korneelverraes/Ctrl-Wheely-2.0/software/album_a.jpg

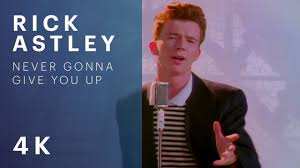
software/album_a.jpg
