korneelverraes/Ctrl-Wheely-2.0/software/album_b.jpg

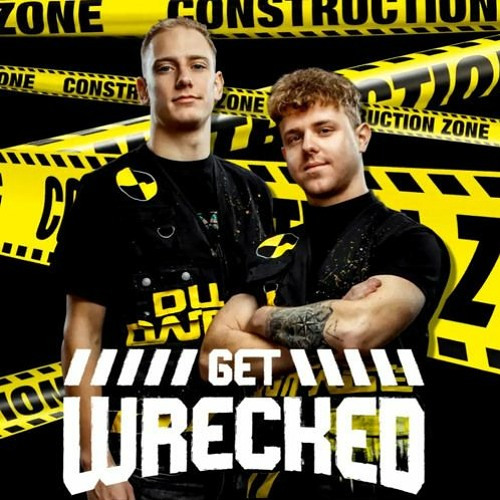
software/album_b.jpg
