korneelverraes/Ctrl-Wheely-2.0/software/album_e.png

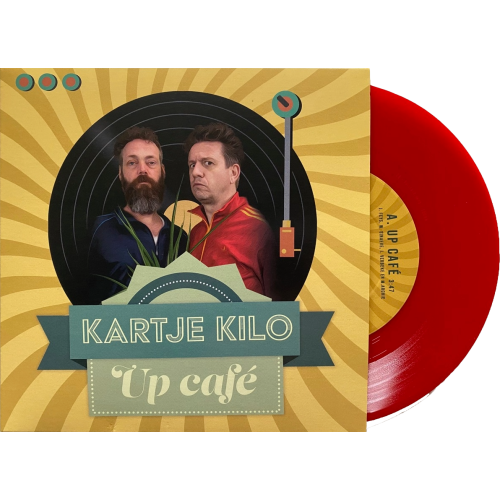
software/album_e.png
