korneelverraes/Ctrl-Wheely-2.0/software/carseat.png

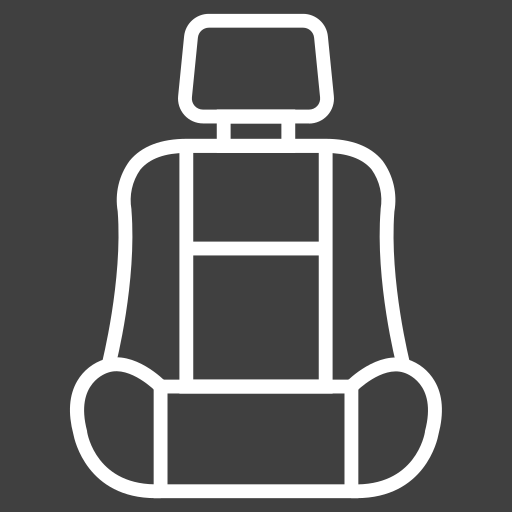
software/carseat.png
