korneelverraes/Ctrl-Wheely-2.0/software/finish.png

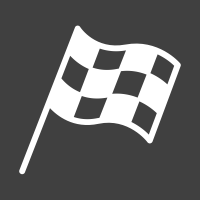
software/finish.png
