korneelverraes/Ctrl-Wheely-2.0/software/HardPress.png

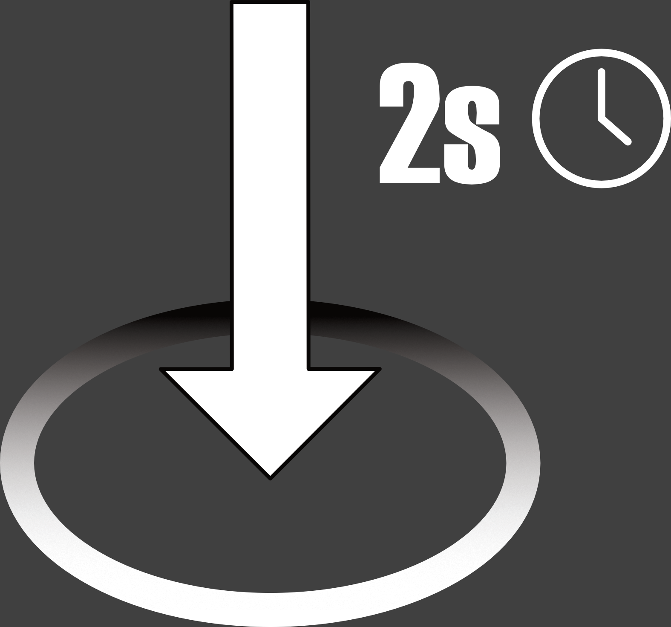
software/HardPress.png
