korneelverraes/Ctrl-Wheely-2.0/software/HardPress_ruitventil.png

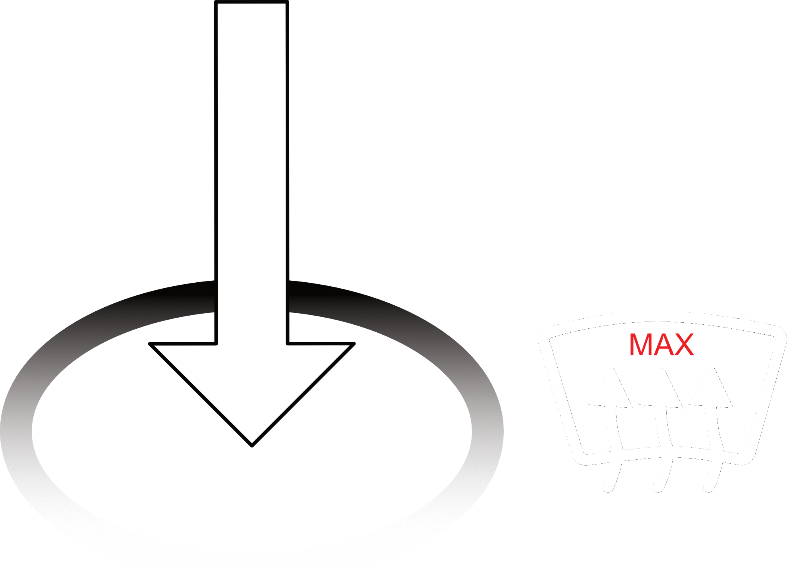
software/HardPress_ruitventil.png
