korneelverraes/Ctrl-Wheely-2.0/software/maxsnel.png

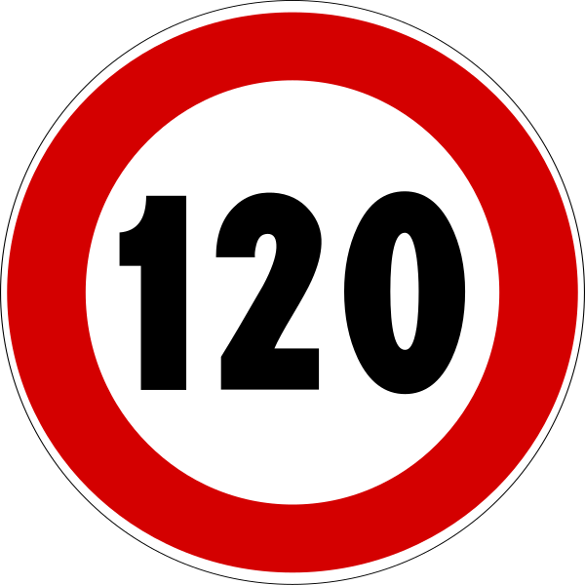
software/maxsnel.png
