korneelverraes/Ctrl-Wheely-2.0/software/micro.png

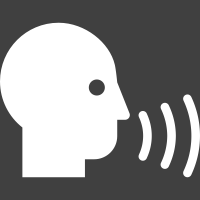
software/micro.png
