korneelverraes/Ctrl-Wheely-2.0/software/pos.music.png

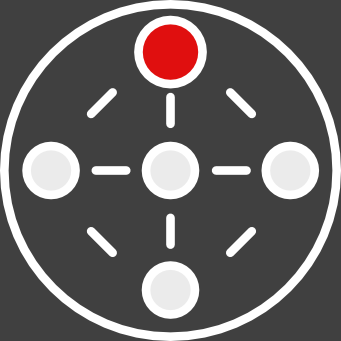
software/pos.music.png
