korneelverraes/Ctrl-Wheely-2.0/software/pos.nav2.png

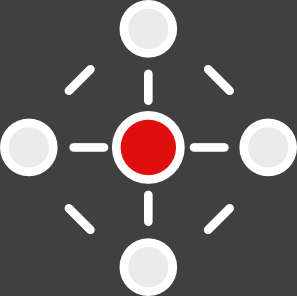
software/pos.nav2.png
