korneelverraes/Ctrl-Wheely-2.0/software/pos.nav3.png

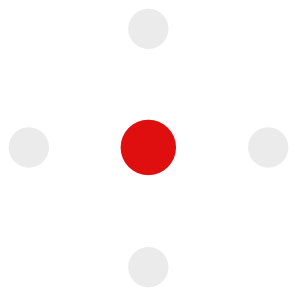
software/pos.nav3.png
