korneelverraes/Ctrl-Wheely-2.0/software/pos.tempL.png

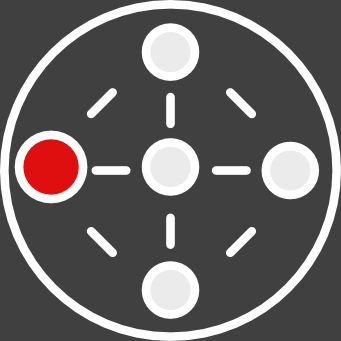
software/pos.tempL.png
