korneelverraes/Ctrl-Wheely-2.0/software/pos.tempR.png

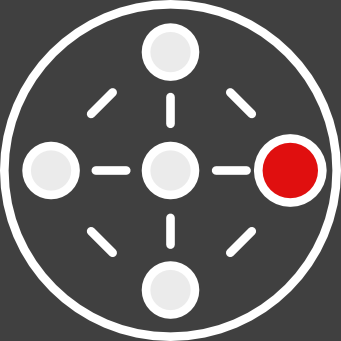
software/pos.tempR.png
