korneelverraes/Ctrl-Wheely-2.0/software/ruitventil.png

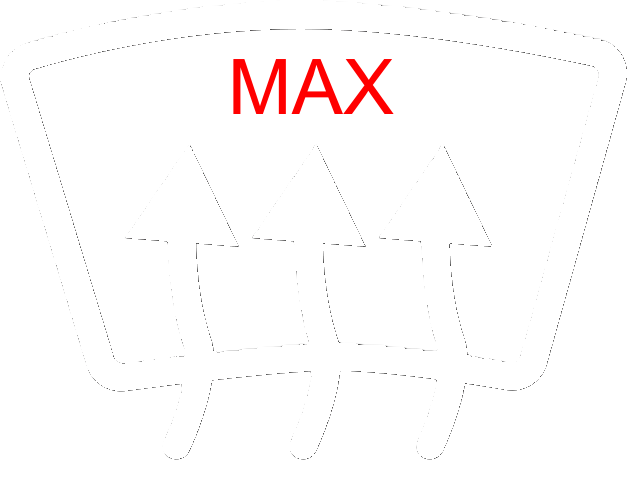
software/ruitventil.png
