korneelverraes/Ctrl-Wheely-2.0/software/ventilatie.png

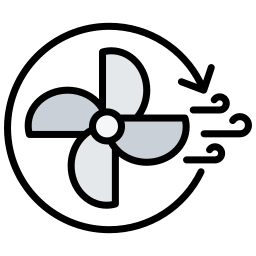
software/ventilatie.png
